VandeputteArne/BrainMoveG1/docs/images/games-grid.png

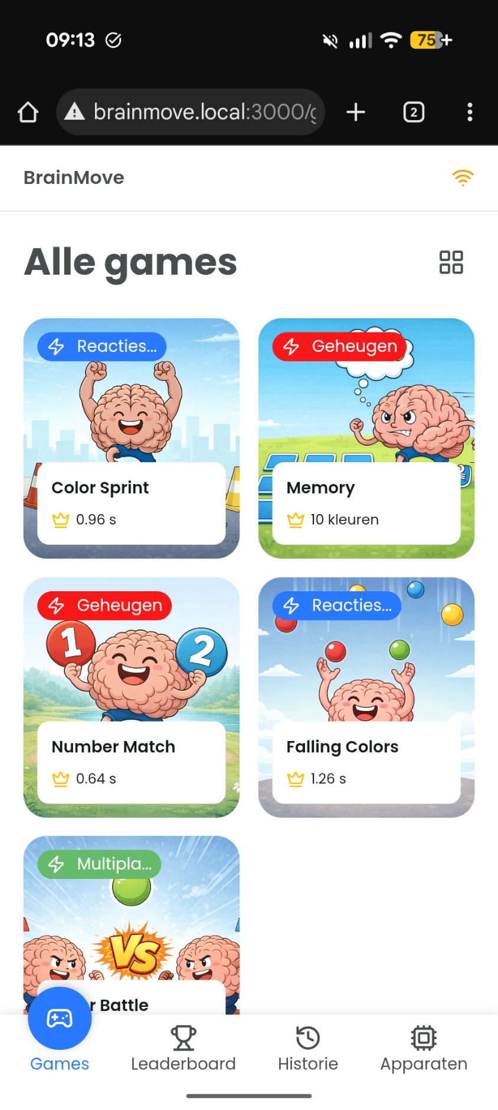
docs/images/games-grid.png
