VandeputteArne/BrainMoveG1/docs/images/games-leaderboard.png

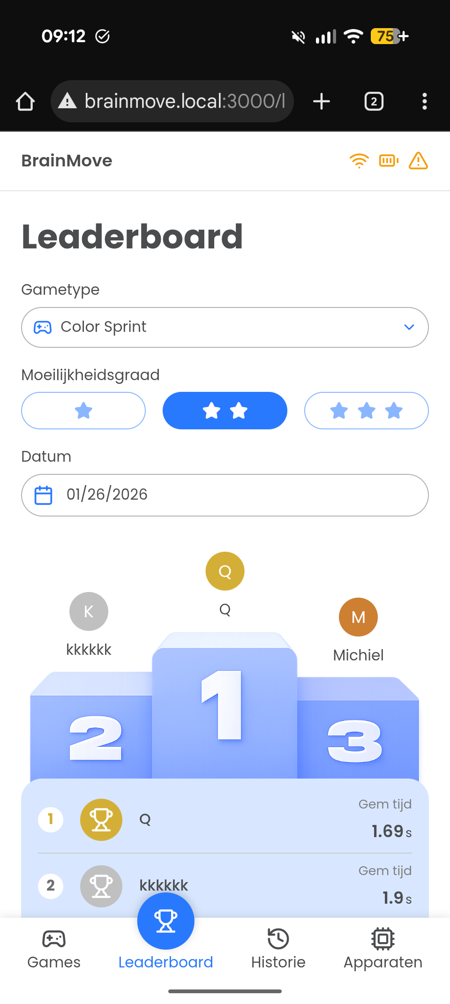
docs/images/games-leaderboard.png
